techniker/magicshifteros/Firmware/MyMain.cpp

/*
 * GccApplication1.cpp
 *
 * Created: 14.02.2014 21:14:44
 *  Author: Daniel
 */ 


//#include <avr/io.h>
#define ARDUINO_MAIN

//#include <Arduino.h>
#include "firmware.h"


int main(void);
/*{
	init();

	#if defined(USBCON)
	USBDevice.attach();
	#endif
	
	setup();
	
	for (;;) {
		loop();
		if (serialEventRun) serialEventRun();
	}
	
	return 0;
}*/
